Upcycle-Electronics/game-and-watch-hardware/Extra-Art/blankfront.jpg

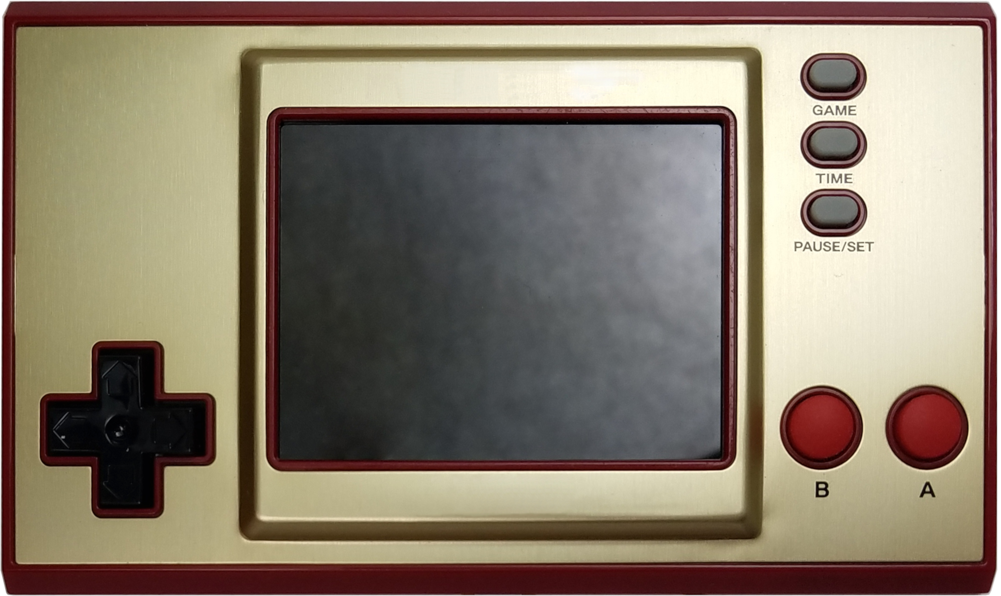
Extra-Art/blankfront.jpg
