Upcycle-Electronics/game-and-watch-hardware/Extra-Art/stm32hb-seethru-trace.jpg

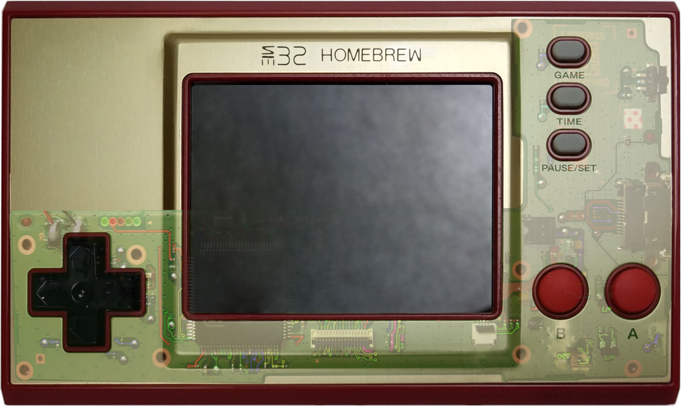
Extra-Art/stm32hb-seethru-trace.jpg
