Upcycle-Electronics/game-and-watch-hardware/gimp/board-pics/G&W USB cnt.jpg

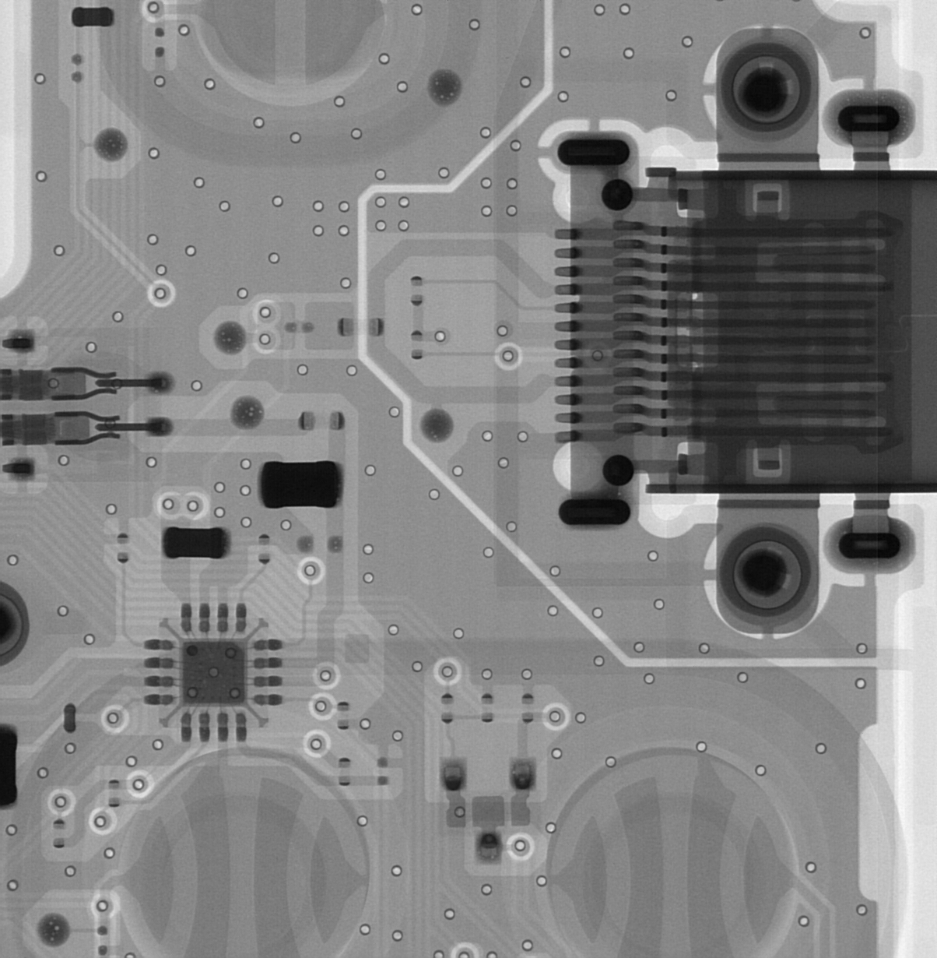
gimp/board-pics/G&W USB cnt.jpg
