Upcycle-Electronics/game-and-watch-hardware/Images-Version-Current/final-trace/GnWtrace-master-xray0.png

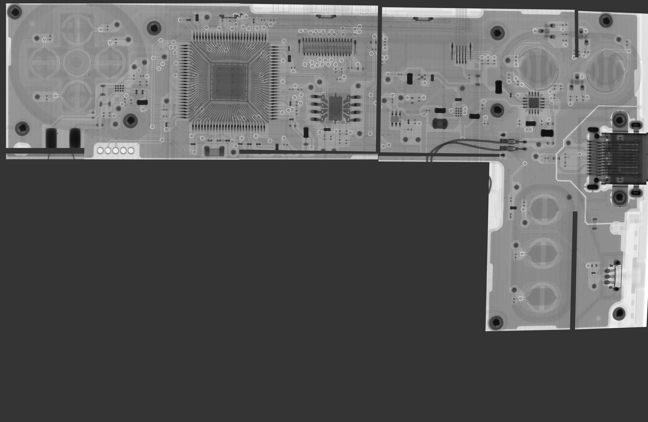
Images-Version-Current/final-trace/GnWtrace-master-xray0.png
